William-Ao/SDVX-Keyboard-Controller/controller_v0.3/3D_Files/Designs/sdvx_encoder_connector.FCStd

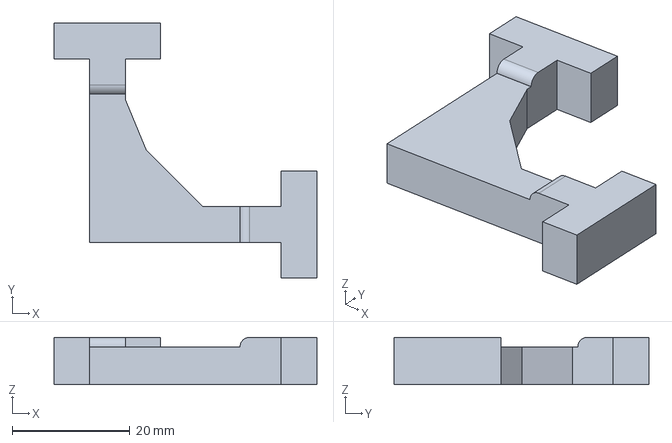
[picture p15: CAD file, 2025-06-27]
controller_v0.3/3D_Files/Designs/sdvx_encoder_connector.FCStd
44.6 x 43.2 x 8.00 mm
