William-Ao/SDVX-Keyboard-Controller/controller_v0.3/3D_Files/Designs/sdvx_BT_connectors.FCStd

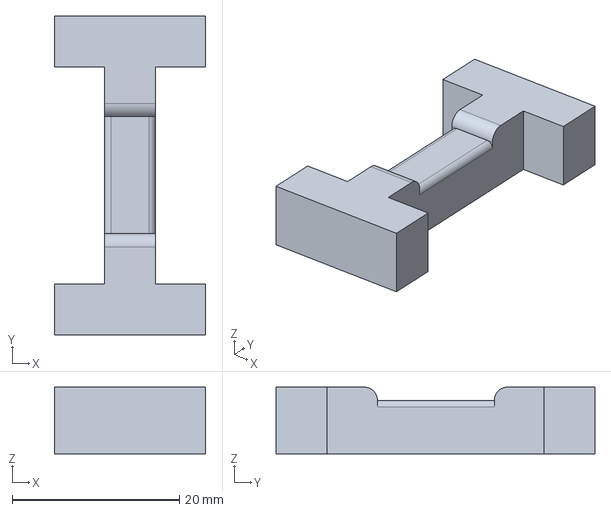
[picture p16: CAD file, 2025-06-27]
controller_v0.3/3D_Files/Designs/sdvx_BT_connectors.FCStd
18.1 x 38.2 x 8.00 mm
