William-Ao/SDVX-Keyboard-Controller/controller_v0.3/3D_Files/sdvx_FX_connector_bent_left.3mf

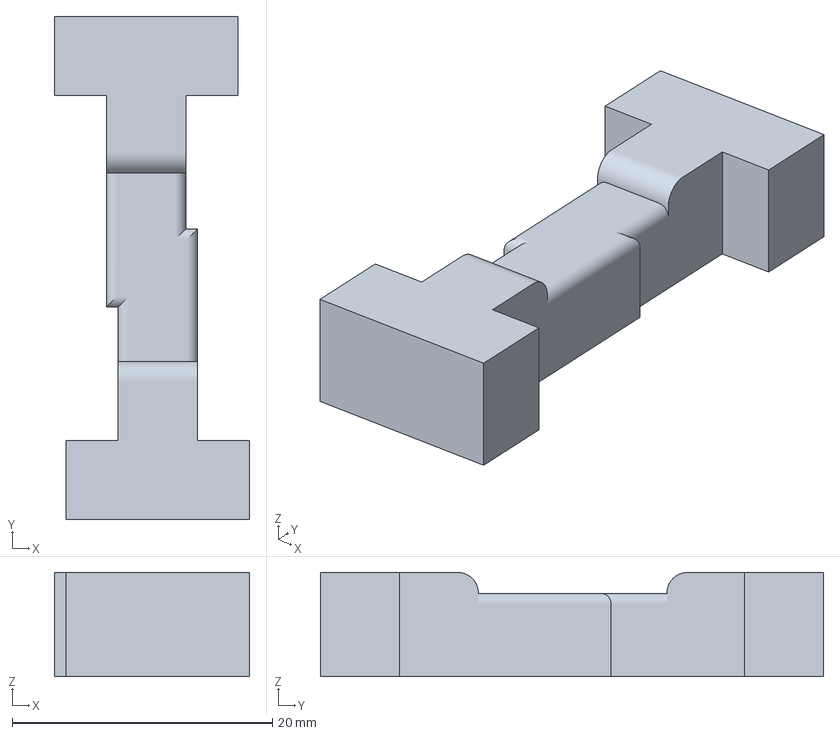
[picture p17: CAD file, 2025-06-27]
controller_v0.3/3D_Files/sdvx_FX_connector_bent_left.3mf
15.0 x 38.7 x 8.00 mm
