William-Ao/SDVX-Keyboard-Controller/controller_v0.3/3D_Files/Designs/plate_tolerance.FCStd

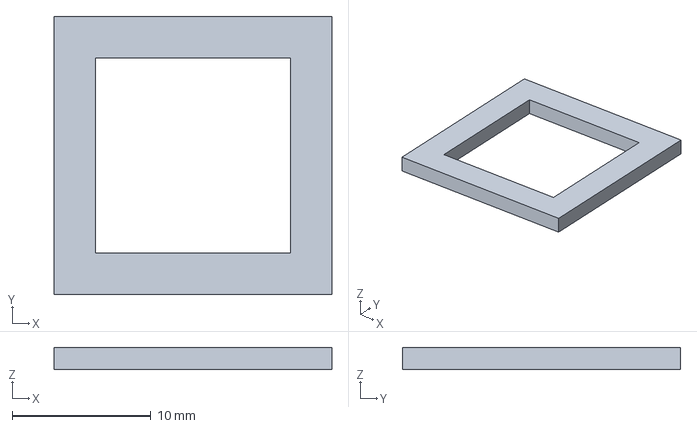
[picture p18: CAD file, 2025-06-27]
controller_v0.3/3D_Files/Designs/plate_tolerance.FCStd
20.0 x 20.0 x 1.60 mm
