William-Ao/SDVX-Keyboard-Controller/controller_v0.3/3D_Files/Designs/sdvx_FX_connector_bent.FCStd

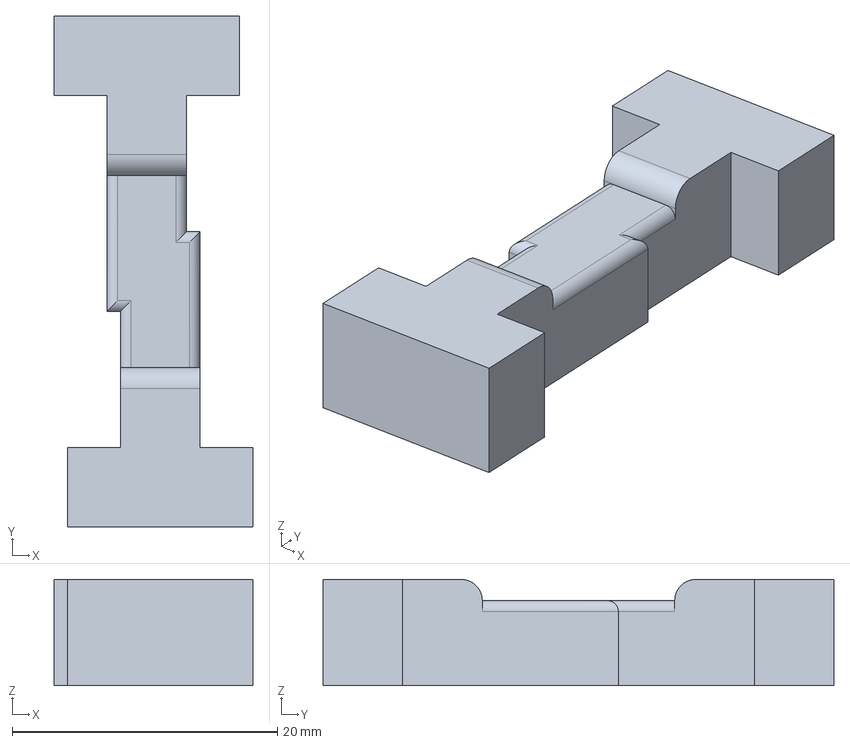
[picture p19: CAD file, 2025-03-01]
controller_v0.3/3D_Files/Designs/sdvx_FX_connector_bent.FCStd
15.0 x 38.5 x 8.00 mm
