William-Ao/SDVX-Keyboard-Controller/controller_v0.3/3D_Files/Designs/sdvx_buttons_housing.FCStd

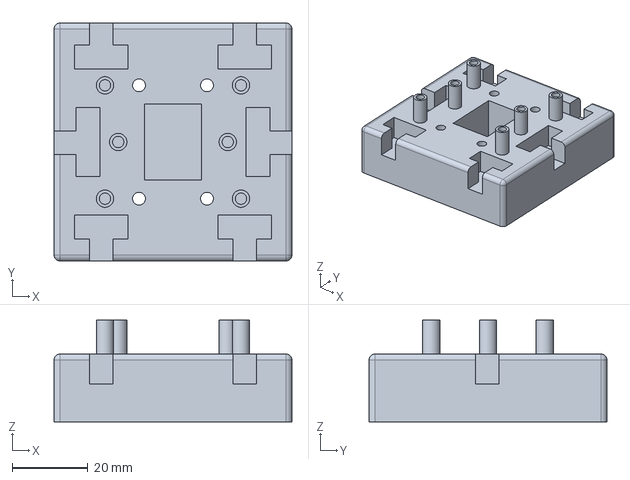
[picture p20: CAD file, 2025-03-01]
controller_v0.3/3D_Files/Designs/sdvx_buttons_housing.FCStd
63.0 x 63.0 x 27.0 mm
