William-Ao/SDVX-Keyboard-Controller/controller_v0.3/3D_Files/Designs/stem_tolerance_tester.FCStd

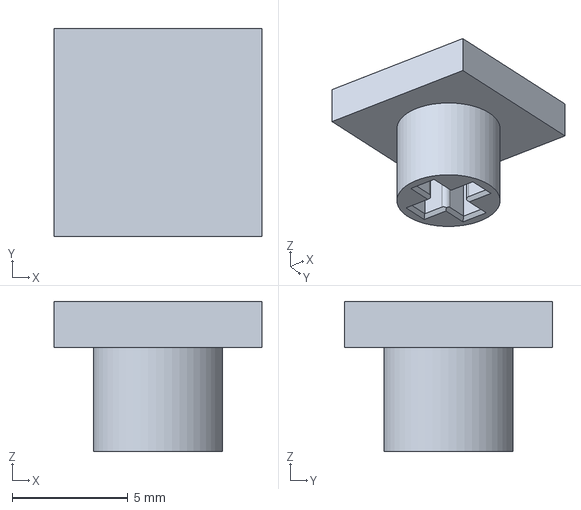
[picture p21: CAD file, 2025-03-01]
controller_v0.3/3D_Files/Designs/stem_tolerance_tester.FCStd
9.00 x 9.00 x 6.50 mm
