William-Ao/SDVX-Keyboard-Controller/controller_v0.3/3D_Files/Designs/sdvx_FX_connectors.FCStd

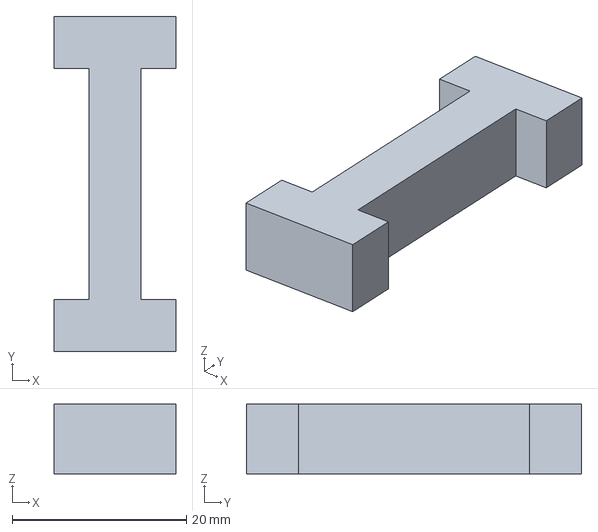
[picture p22: CAD file, 2025-02-27]
controller_v0.3/3D_Files/Designs/sdvx_FX_connectors.FCStd
14.0 x 38.5 x 8.00 mm
